squares/BB8/images/Board1-NoHeaders.jpg

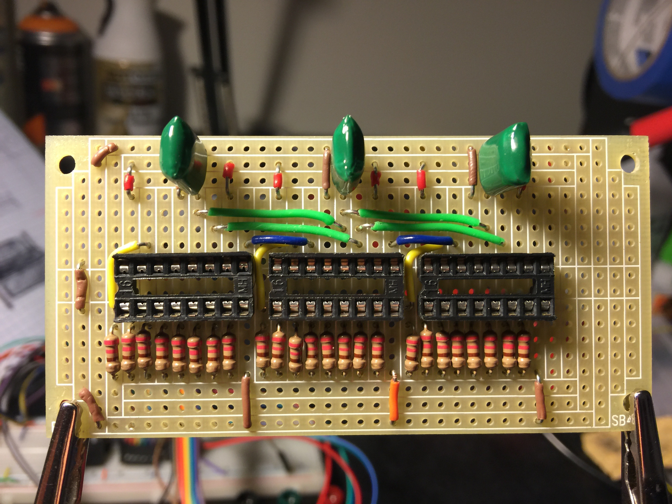
images/Board1-NoHeaders.jpg
