squares/BB8/images/Board2-Completed.jpg

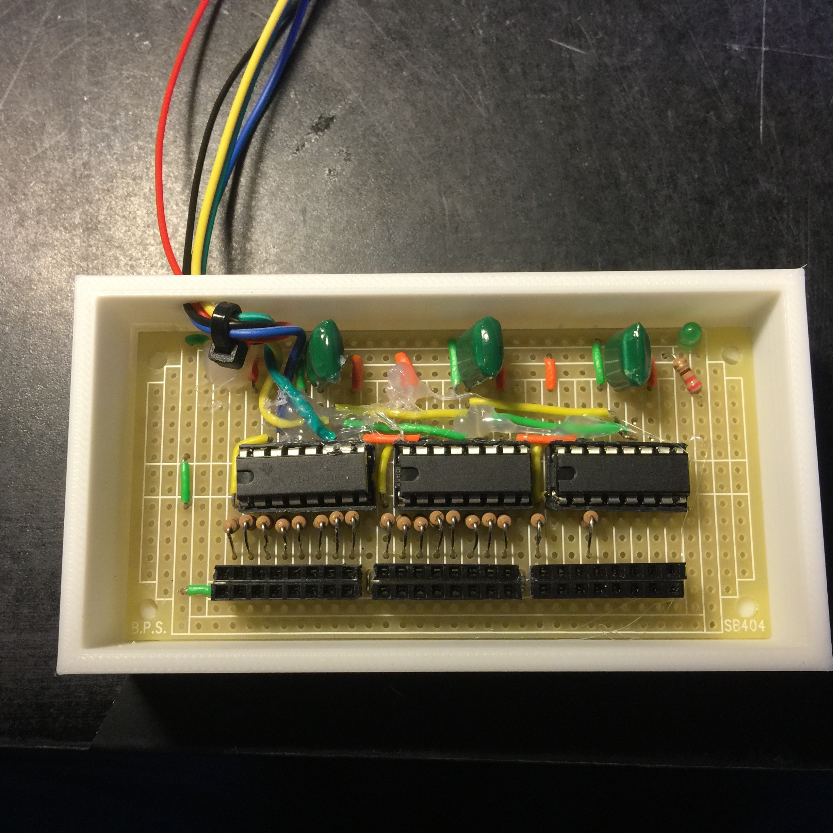
images/Board2-Completed.jpg
