squares/BB8/images/FinishedModule2.jpg

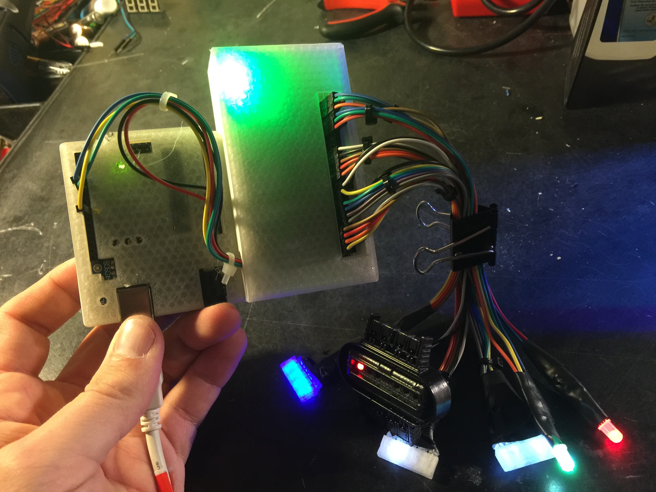
images/FinishedModule2.jpg
