squares/BB8/images/FinishedModule.jpg

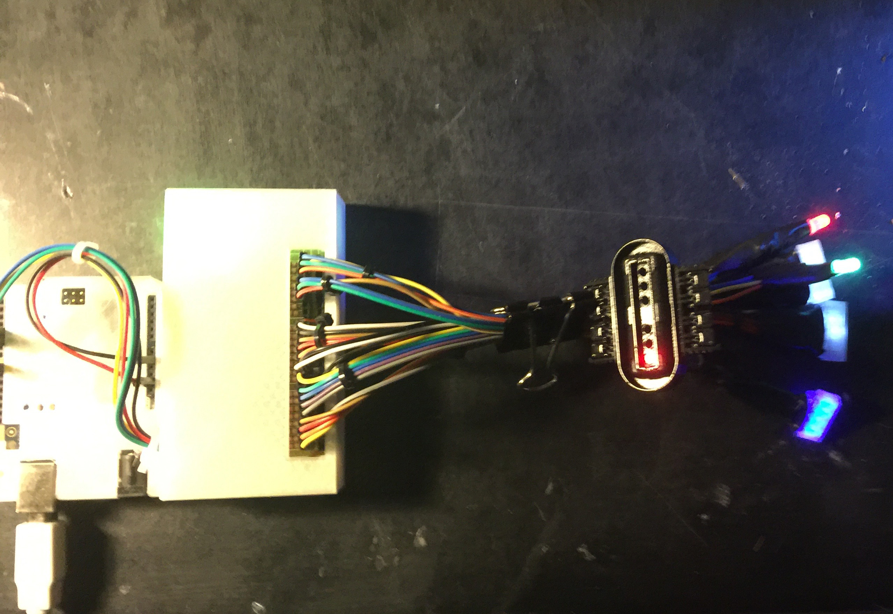
images/FinishedModule.jpg
