squares/BB8/images/IC-Indent.jpg

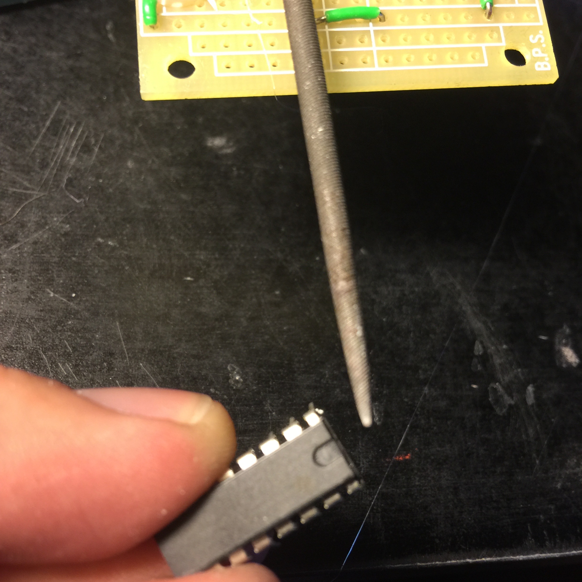
images/IC-Indent.jpg
