squares/BB8/images/MagnifyingLens.jpg

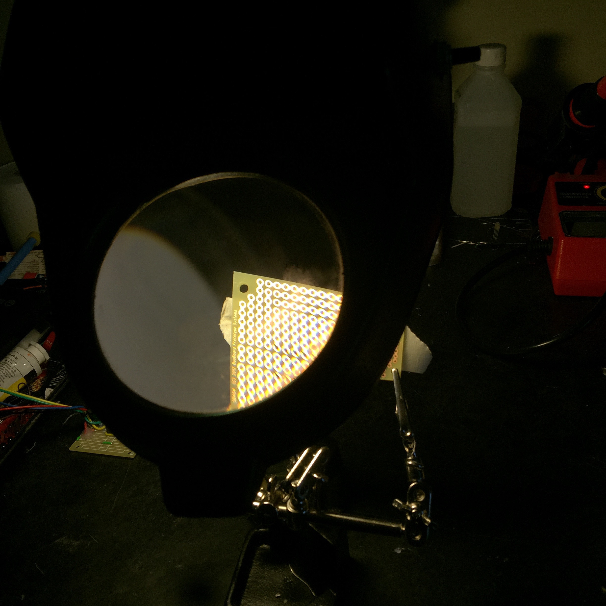
images/MagnifyingLens.jpg
