squares/BB8/images/Radar-GluedLED.jpg

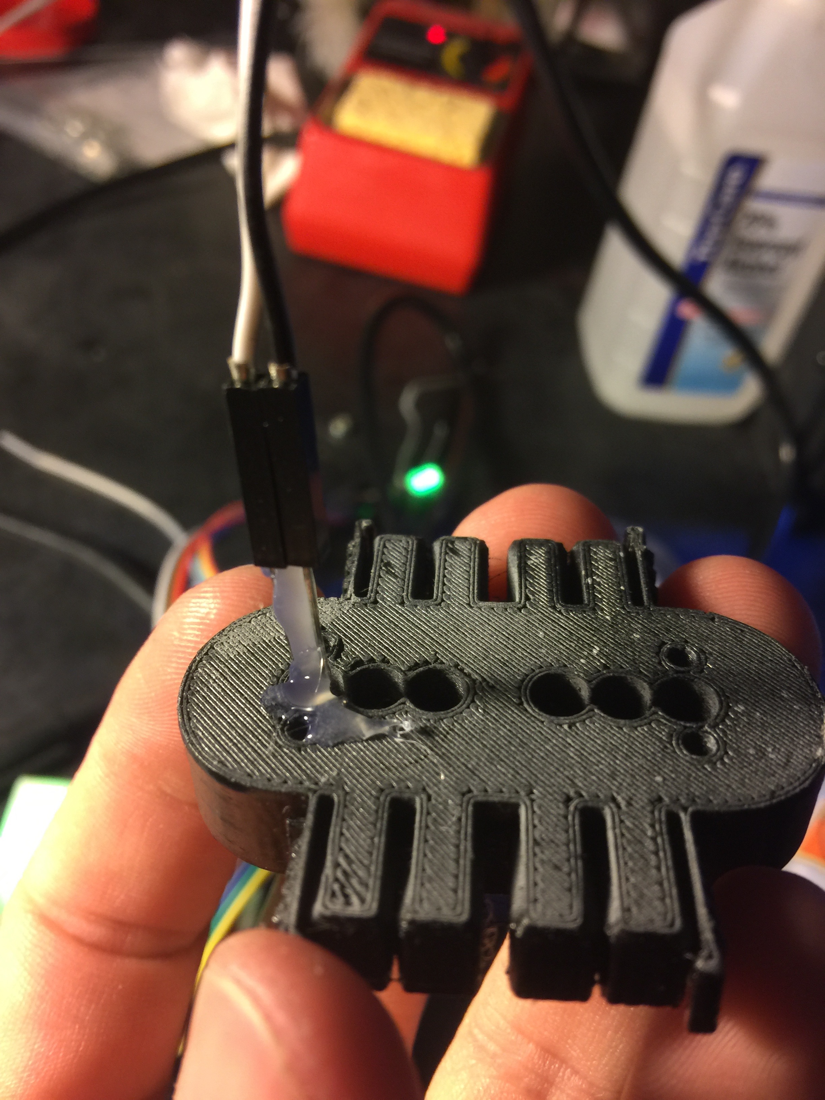
images/Radar-GluedLED.jpg
