squares/BB8/images/Resistors-bent.jpg

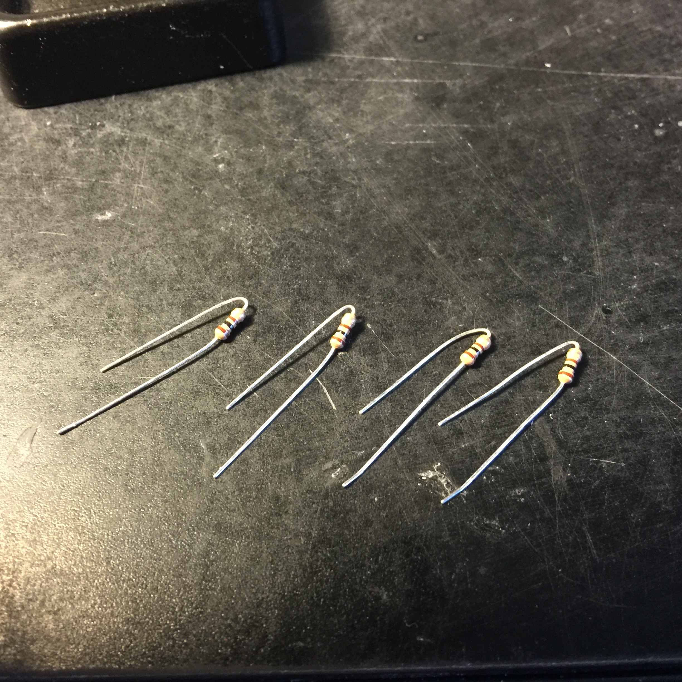
images/Resistors-bent.jpg
