squares/BB8/Schematic.png

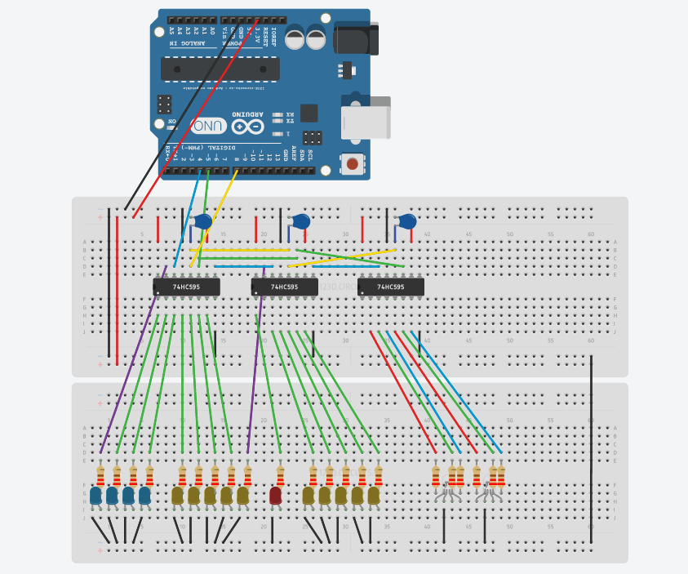
Schematic.png
