squares/BB8/images/InstalledModule.jpg

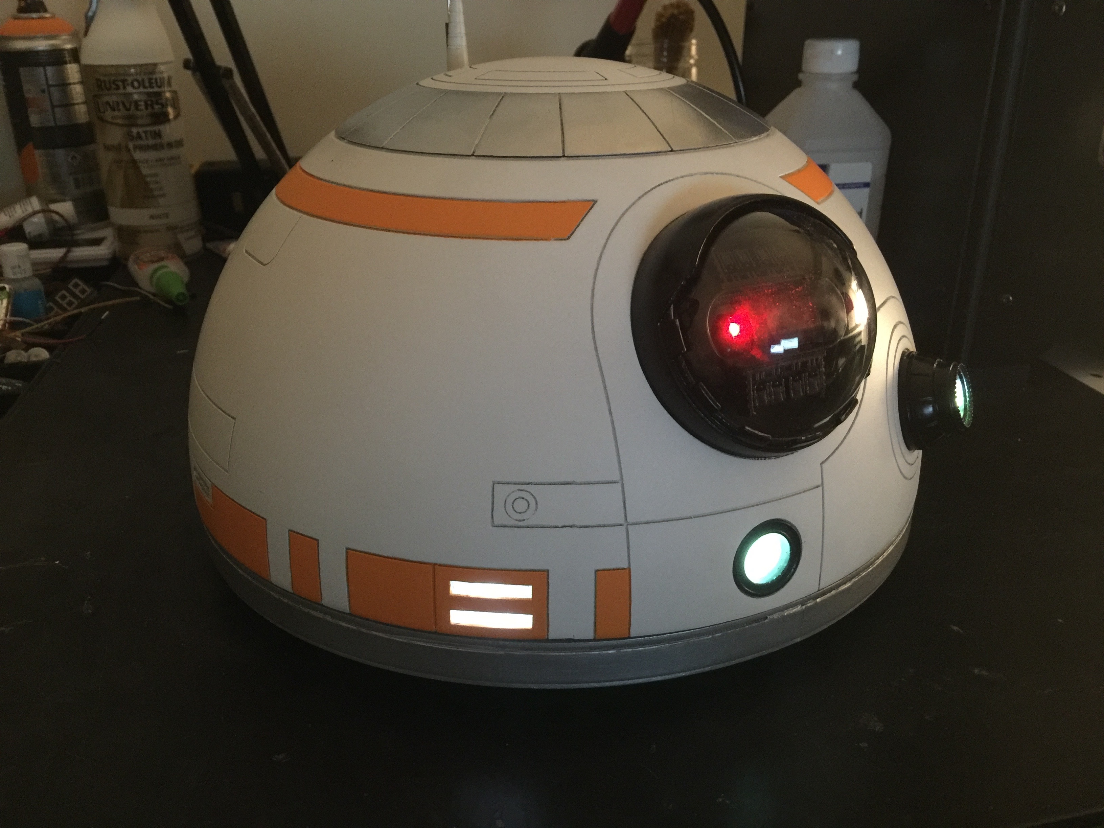
images/InstalledModule.jpg
