squares/BB8/images/Step11B.jpg

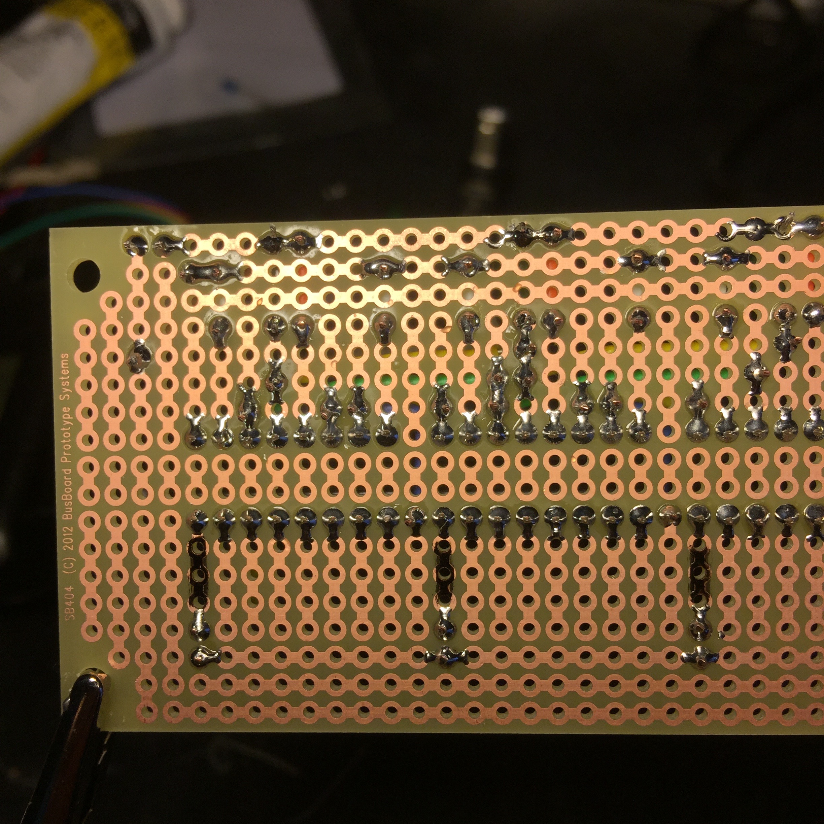
images/Step11B.jpg
