squares/BB8/images/Step14C.jpg

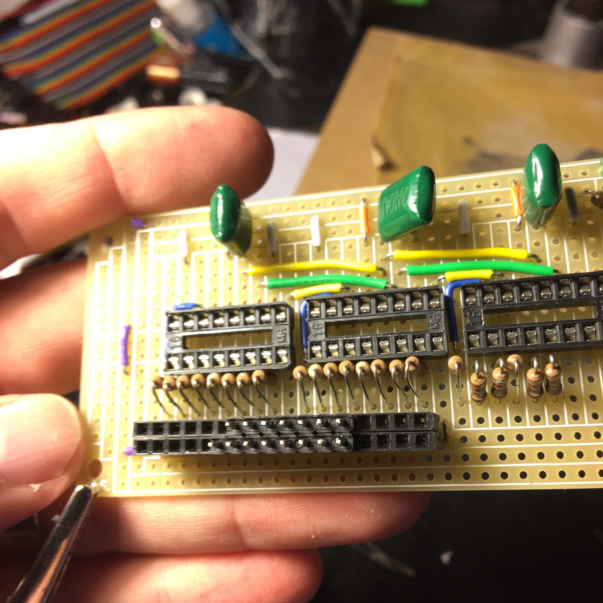
images/Step14C.jpg
